millerlp/MusselTracker/Test_sketches/LSM303_output/LSM303_output.ino

/*
The sensor outputs provided by the library are the raw 16-bit values
obtained by concatenating the 8-bit high and low accelerometer and
magnetometer data registers. They can be converted to units of g and
gauss using the conversion factors specified in the datasheet for your
particular device and full scale setting (gain).

Example: An LSM303D gives a magnetometer X axis reading of 1982 with
its default full scale setting of +/- 4 gauss. The M_GN specification
in the LSM303D datasheet (page 10) states a conversion factor of 0.160
mgauss/LSB (least significant bit) at this FS setting, so the raw
reading of -1982 corresponds to 1982 * 0.160 = 317.1 mgauss =
0.3171 gauss.


*/

#include <Wire.h>
#include <LSM303.h>

LSM303 compass;

char report[80];

void setup()
{
  Serial.begin(57600);
  Wire.begin();
  compass.init();
  compass.enableDefault();
}

void loop()
{
  compass.read();

  snprintf(report, sizeof(report), "%6d,%6d,%6d,%6d,%6d,%6d",
    compass.a.x, compass.a.y, compass.a.z,
    compass.m.x, compass.m.y, compass.m.z);
  Serial.println(report);

  delay(50);
}
